RT-CUSTOMZ/wortuhr-mini/Bilder/Plottern/1Laptopverbinden.jpg

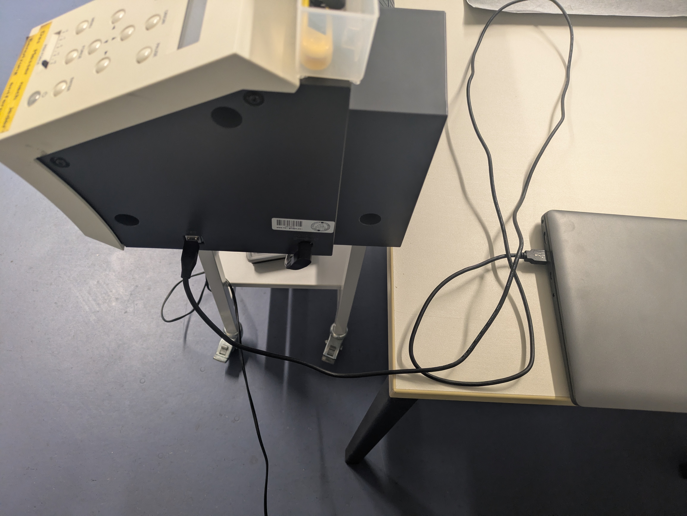
Bilder/Plottern/1Laptopverbinden.jpg
