RT-CUSTOMZ/wortuhr-mini/Bilder/Plottern/4Blatteinlegen1.jpg

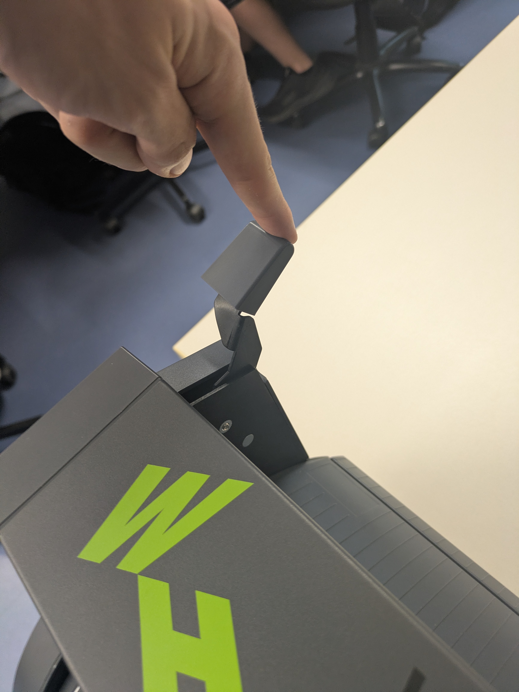
Bilder/Plottern/4Blatteinlegen1.jpg
