RT-CUSTOMZ/wortuhr-mini/Bilder/Plottern/5Blatteinlegen2.jpg

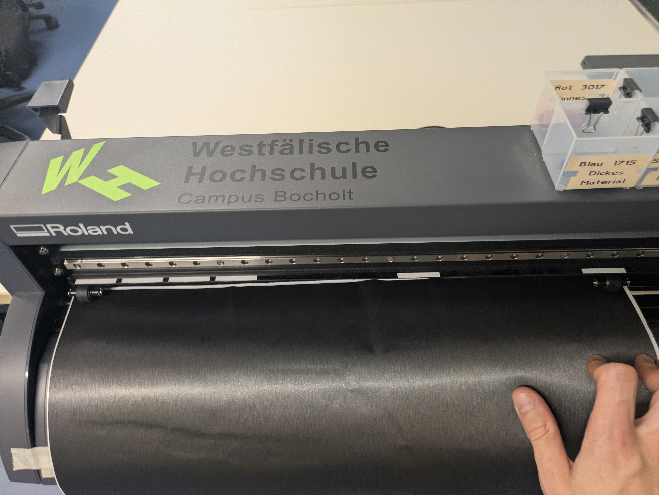
Bilder/Plottern/5Blatteinlegen2.jpg
