RT-CUSTOMZ/wortuhr-mini/Bilder/Plottern/6Blatteinlegen3.jpg

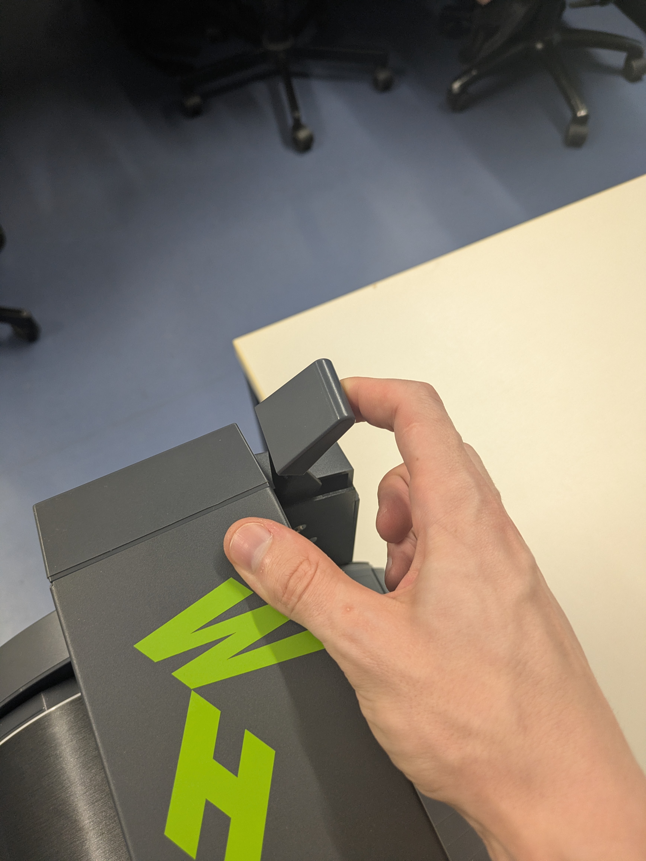
Bilder/Plottern/6Blatteinlegen3.jpg
