RT-CUSTOMZ/wortuhr-mini/Bilder/Plottern/7Blatteinlesen1.jpg

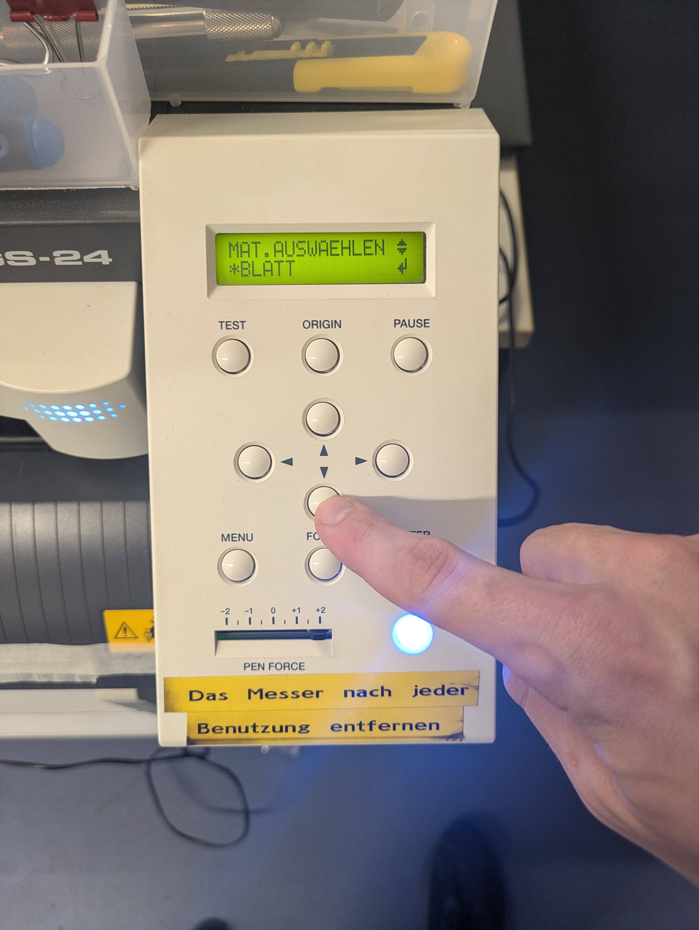
Bilder/Plottern/7Blatteinlesen1.jpg
