RT-CUSTOMZ/wortuhr-mini/Bilder/Plottern/8Blatteinlesen2.jpg

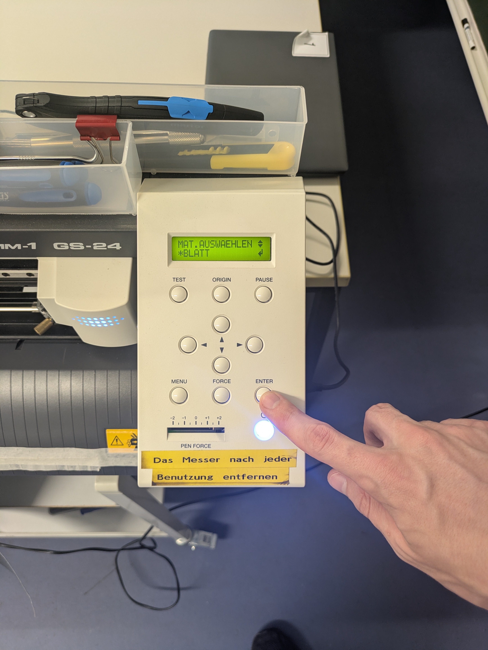
Bilder/Plottern/8Blatteinlesen2.jpg
