RT-CUSTOMZ/wortuhr-mini/Bilder/Plottern/12Plottern_1.png

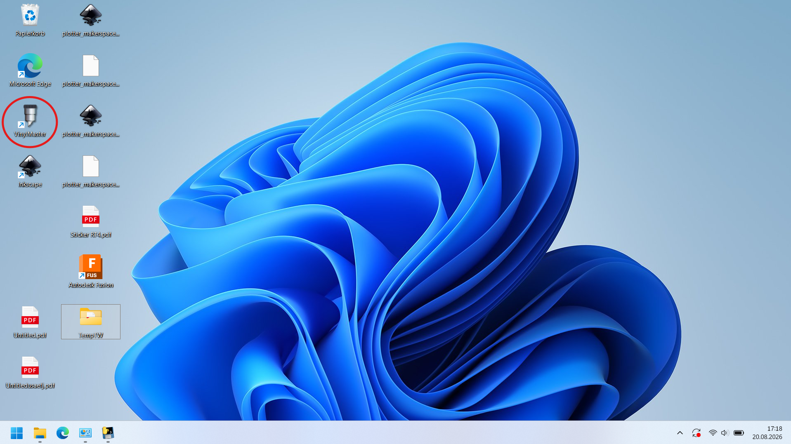
Bilder/Plottern/12Plottern_1.png
