RT-CUSTOMZ/wortuhr-mini/Bilder/Plottern/16Plottern_5.png

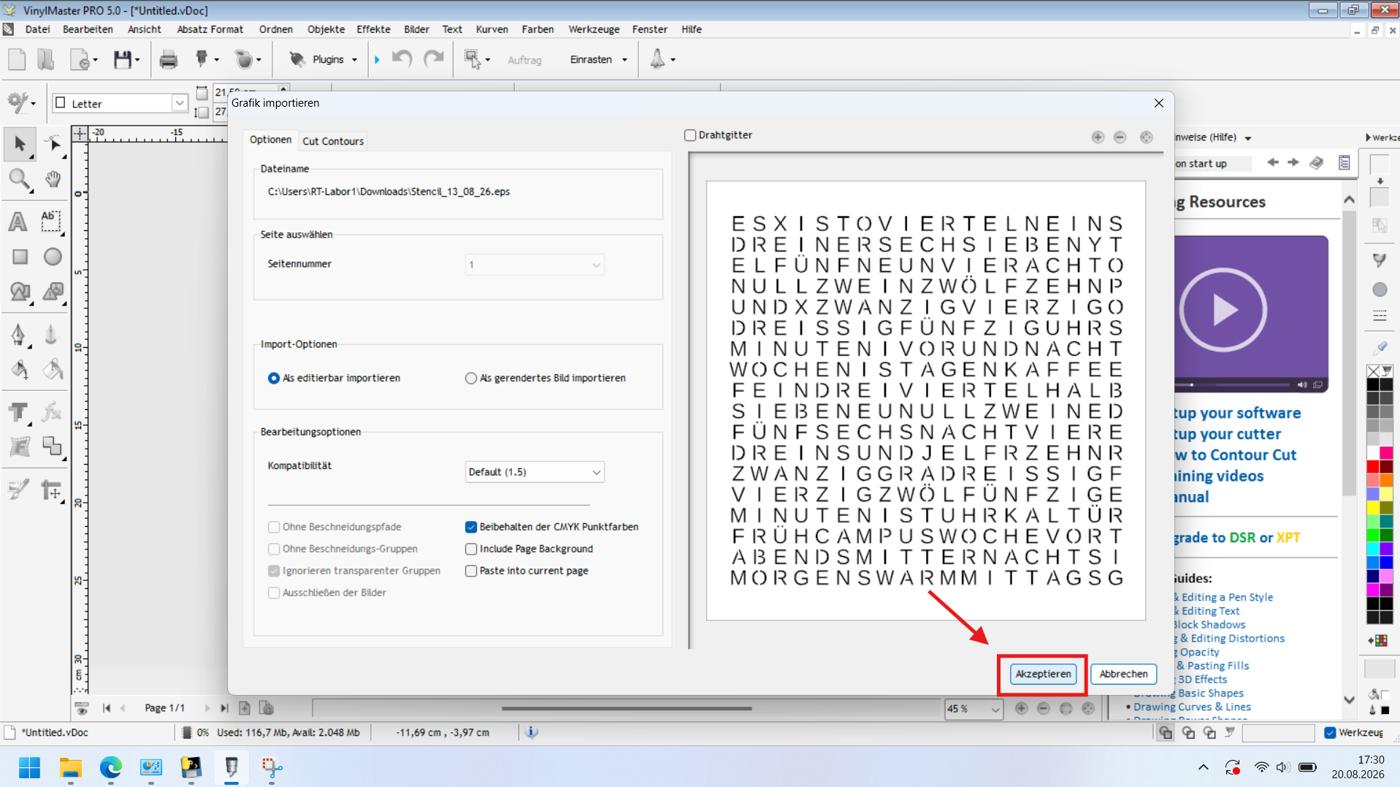
Bilder/Plottern/16Plottern_5.png
