RT-CUSTOMZ/wortuhr-mini/Bilder/Plottern/18Plottern_7.png

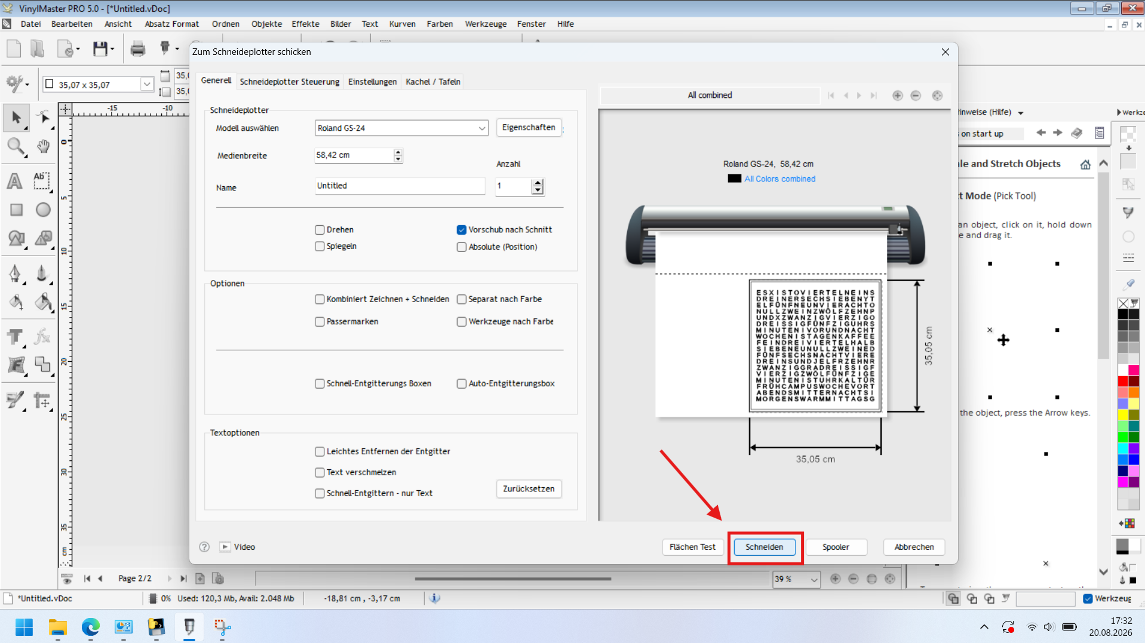
Bilder/Plottern/18Plottern_7.png
