RT-CUSTOMZ/wortuhr-mini/Bauanleitung/Orthogonal Top.png

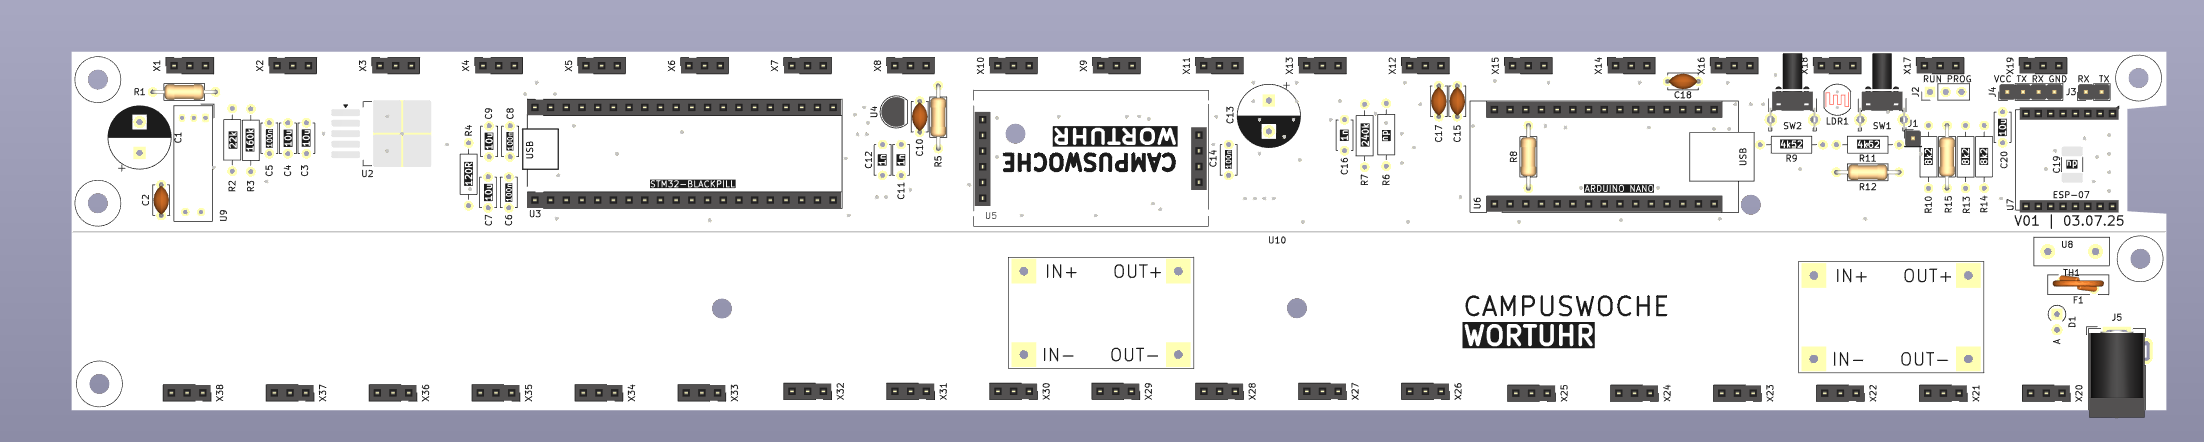
Bauanleitung/Orthogonal Top.png
