RT-CUSTOMZ/wortuhr-mini/Bauanleitung/Ortogonal Side.png

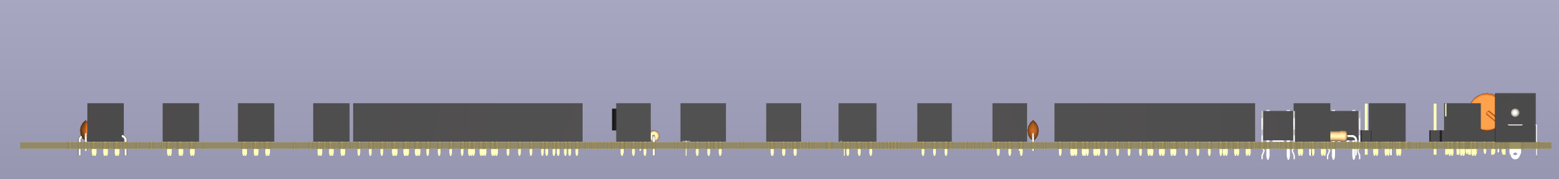
Bauanleitung/Ortogonal Side.png
