RT-CUSTOMZ/wortuhr-mini/Bilder/Plottern/10Test2.jpg

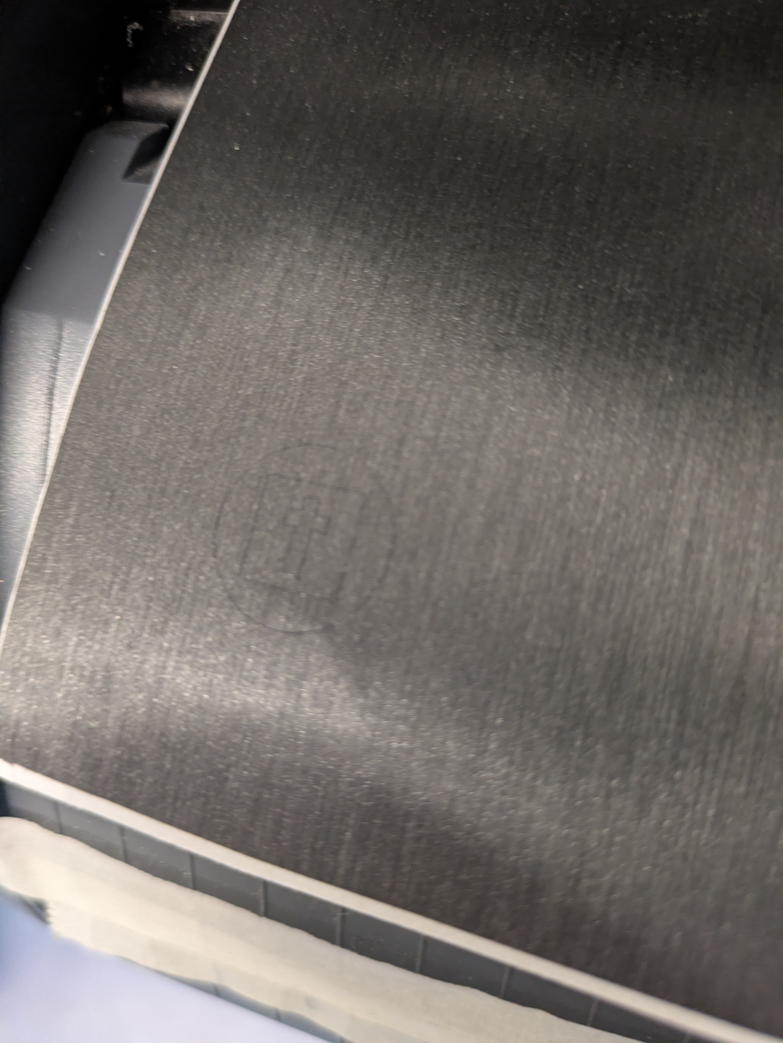
Bilder/Plottern/10Test2.jpg
