RT-CUSTOMZ/wortuhr-mini/Bilder/Plottern/11Test3.jpg

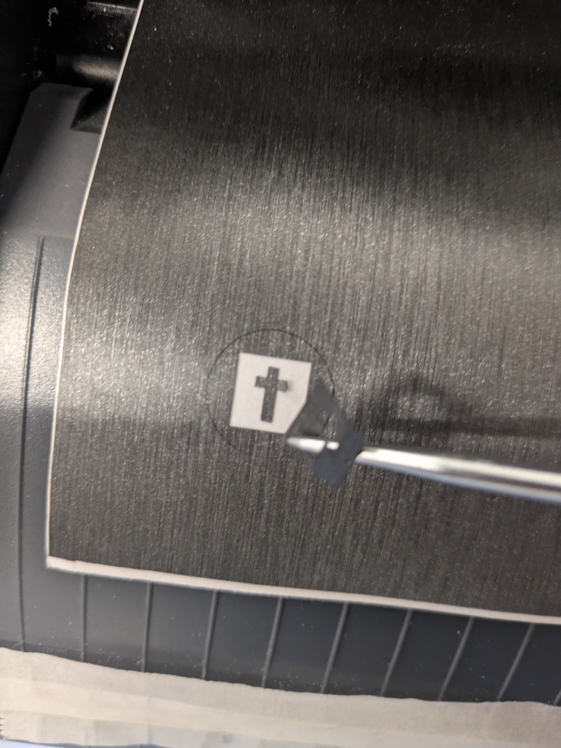
Bilder/Plottern/11Test3.jpg
